VasilKalchev/ATmega328-SPI_test_board/eagleUp/eagleUp_nRF24L01+ - ATmega328 test board_bottom_silk.png

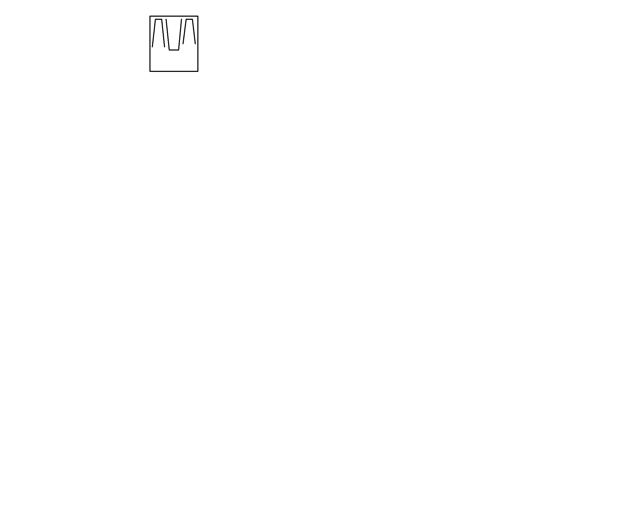
eagleUp/eagleUp_nRF24L01+ - ATmega328 test board_bottom_silk.png
